avin-c/keeboard/journal-pics/image-22.png

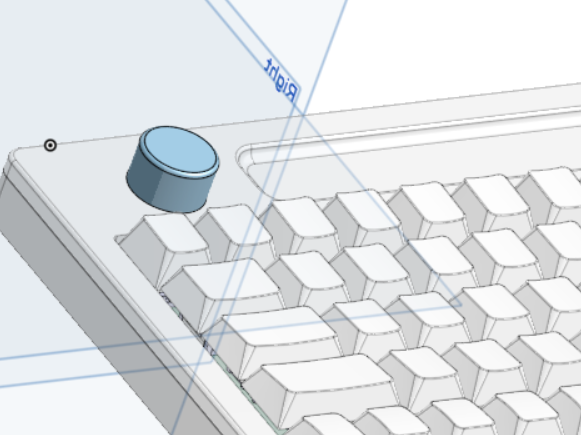
journal-pics/image-22.png
