avin-c/keeboard/journal-pics/image-29.png

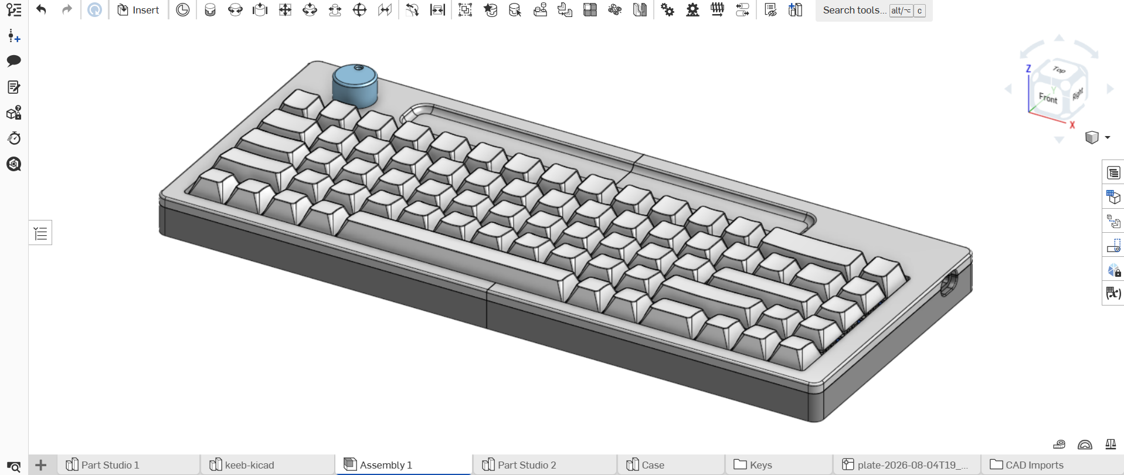
journal-pics/image-29.png
